fgonzalop/boxcontrol/InitNode/CalefaccionP0.h

const String THE_NAME     = "CALEFACCION P0";
const int THE_RADIO_ID    = 1;
const int THE_RELAY_INDEX = 8;
const int THE_RELAY_0     = 17;
const int THE_RELAY_1     = 8;
const int THE_RELAY_2     = 7;
const int THE_RELAY_3     = 6;
const int THE_RELAY_4     = 5;
const int THE_RELAY_5     = 4;
const int THE_RELAY_6     = 3;
const int THE_RELAY_7     = 2;
const int THE_RELAY_8     = 255;
const int THE_RELAY_9     = 255;
const int THE_TEMPERATURE_PIN = 255;
const int THE_PIR_PIN     = 255;
const int THE_LUX_PIN     = 255;

// tbd "relay_off":"LOW",
