fgonzalop/boxcontrol/InitNode/Cochera.h

const String THE_NAME     = "COCHERA";
const int THE_RADIO_ID    = 3;
const int THE_RELAY_INDEX = 255;
const int THE_RELAY_0     = 255;
const int THE_RELAY_1     = 255;
const int THE_RELAY_2     = 255;
const int THE_RELAY_3     = 255;
const int THE_RELAY_4     = 255;
const int THE_RELAY_5     = 255;
const int THE_RELAY_6     = 255;
const int THE_RELAY_7     = 255;
const int THE_RELAY_8     = 255;
const int THE_RELAY_9     = 255;
const int THE_TEMPERATURE_PIN = 4;
const int THE_PIR_PIN     = 3;
const int THE_LUX_PIN     = 7;

// tbd "relay_off":"LOW",
